elezbyl/usb-hub/hw/mcu.kicad_sch

## KiCad design hw/mcu.kicad_sch (2024-12-16)

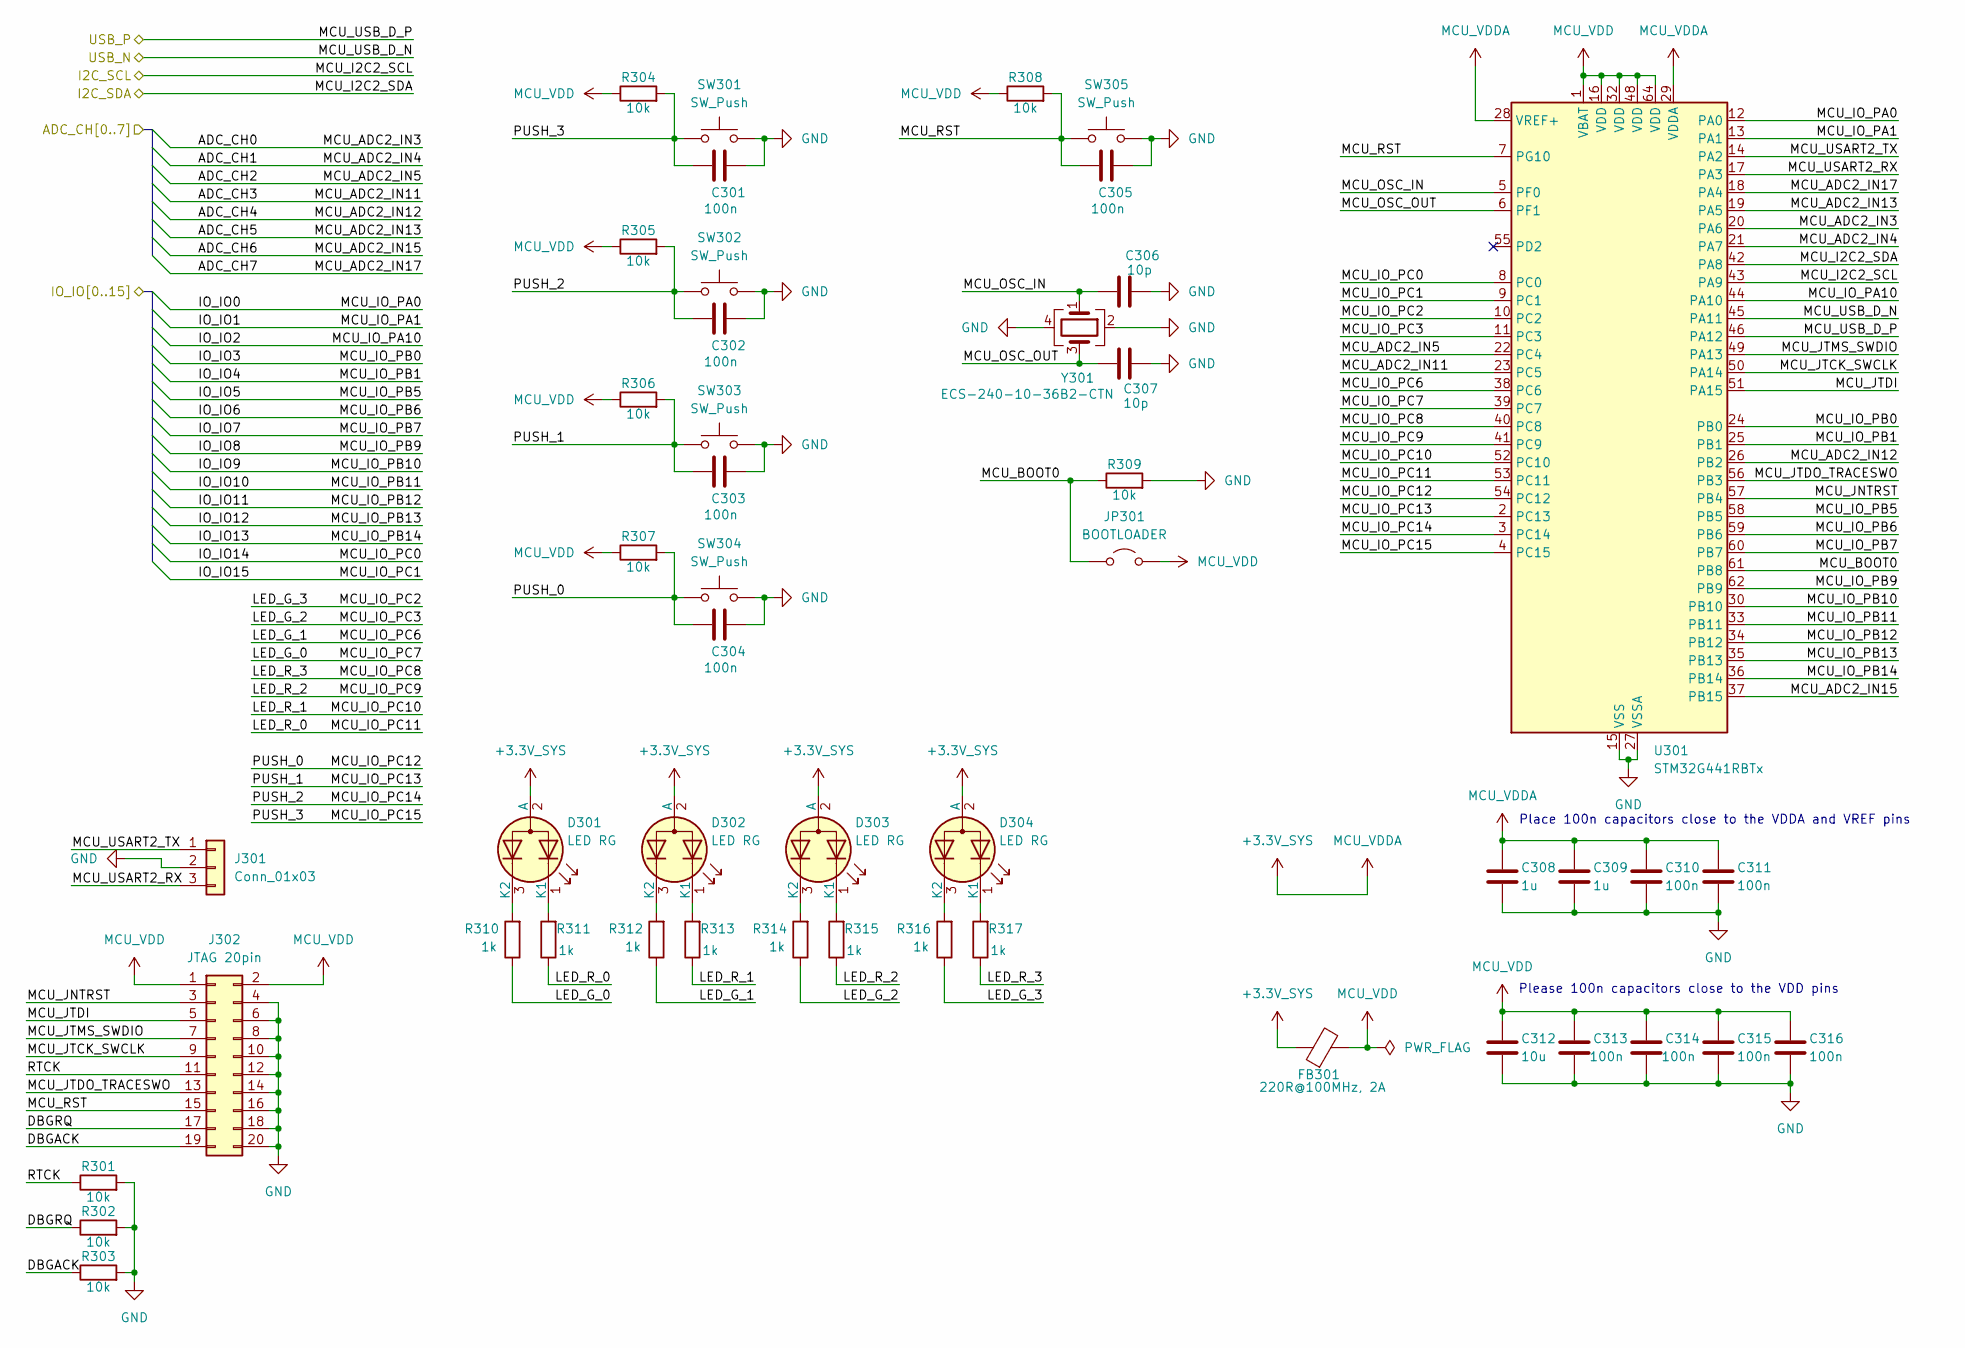
[picture p2: schematic mcu.kicad_sch]

Parts:
C301, C302, C303, C304, C305, C310, C311, C313, C314, C315, C316: 100n; C_0603_1608Metric_Pad1.08x0.95mm_HandSolder
C306, C307: 10p; C_0603_1608Metric_Pad1.08x0.95mm_HandSolder
C308, C309: 1u; C_0603_1608Metric_Pad1.08x0.95mm_HandSolder
C312: 10u; C_0805_2012Metric_Pad1.18x1.45mm_HandSolder
D301, D302, D303, D304: LED RG; LED_Wurth_155124RV73200; Farnell 2764997
FB301: 220R@100MHz, 2A; L_0805_2012Metric_Pad1.05x1.20mm_HandSolder; Farnell 1515661
J301: Conn_01x03; PinHeader_1x03_P2.54mm_Vertical
J302: JTAG 20pin; PinHeader_2x10_P2.54mm_Vertical
JP301: BOOTLOADER; PinHeader_1x02_P2.54mm_Vertical
R301, R302, R303, R304, R305, R306, R307, R308, R309: 10k; R_0603_1608Metric_Pad0.98x0.95mm_HandSolder
R310, R311, R312, R313, R314, R315, R316, R317: 1k; R_0603_1608Metric_Pad0.98x0.95mm_HandSolder
SW301, SW302, SW303, SW304, SW305: SW_Push; SW_Tactile_SPST_NO_Straight_CK_PTS636Sx25SMTRLFS; Farnell 3780601
U301: STM32G441RBTx; LQFP-64_10x10mm_P0.5mm; Farnell 3132415
Y301: ECS-240-10-36B2-CTN; Oscillator_SMD_ECS-xxx-x-36B2-xxx-4Pin_2.5x2.0mm; Farnell 4059099

Connections:
+3.3V_SYS: C308.1, C309.1, C310.1, C311.1, D301.2 (A), D302.2 (A), D303.2 (A), D304.2 (A), FB301.1, U301.28 (VREF+), U301.29 (VDDA)
ADC_CH0: U301.20 (PA6)
ADC_CH1: U301.21 (PA7)
ADC_CH2: U301.22 (PC4)
ADC_CH3: U301.23 (PC5)
ADC_CH4: U301.26 (PB2)
ADC_CH5: U301.19 (PA5)
ADC_CH6: U301.37 (PB15)
ADC_CH7: U301.18 (PA4)
DBGACK: J302.19, R303.1
DBGRQ: J302.17, R302.1
GND: C301.1, C302.1, C303.1, C304.1, C305.1, C306.1, C307.1, C308.2, C309.2, C310.2, C311.2, C312.2, C313.2, C314.2, C315.2, C316.2, J301.2, J302.4, J302.6, J302.8, J302.10, J302.12, J302.14, J302.16, J302.18, J302.20, R301.2, R302.2, R303.2, R309.2, SW301.2, SW302.2, SW303.2, SW304.2, SW305.2, U301.15 (VSS), U301.27 (VSSA), U301.31 (VSS), U301.47 (VSS), U301.63 (VSS), Y301.2, Y301.4
I2C_SCL: U301.43 (PA9)
I2C_SDA: U301.42 (PA8)
IO_IO0: U301.12 (PA0)
IO_IO1: U301.13 (PA1)
IO_IO2: U301.44 (PA10)
IO_IO3: U301.24 (PB0)
IO_IO4: U301.25 (PB1)
IO_IO5: U301.58 (PB5)
IO_IO6: U301.59 (PB6)
IO_IO7: U301.60 (PB7)
IO_IO8: U301.62 (PB9)
IO_IO9: U301.30 (PB10)
IO_IO10: U301.33 (PB11)
IO_IO11: U301.34 (PB12)
IO_IO12: U301.35 (PB13)
IO_IO13: U301.36 (PB14)
IO_IO14: U301.8 (PC0)
IO_IO15: U301.9 (PC1)
LED_G_0: R310.1, U301.39 (PC7)
LED_G_1: R312.1, U301.38 (PC6)
LED_G_2: R314.1, U301.11 (PC3)
LED_G_3: R316.1, U301.10 (PC2)
LED_R_0: R311.1, U301.53 (PC11)
LED_R_1: R313.1, U301.52 (PC10)
LED_R_2: R315.1, U301.41 (PC9)
LED_R_3: R317.1, U301.40 (PC8)
MCU_BOOT0: JP301.1 (A), R309.1, U301.61 (PB8)
MCU_IO_PC12: C304.2, R307.2, SW304.1, U301.54 (PC12)
MCU_IO_PC13: C303.2, R306.2, SW303.1, U301.2 (PC13)
MCU_IO_PC14: C302.2, R305.2, SW302.1, U301.3 (PC14)
MCU_IO_PC15: C301.2, R304.2, SW301.1, U301.4 (PC15)
MCU_JNTRST: J302.3, U301.57 (PB4)
MCU_JTCK_SWCLK: J302.9, U301.50 (PA14)
MCU_JTDI: J302.5, U301.51 (PA15)
MCU_JTDO_TRACESWO: J302.13, U301.56 (PB3)
MCU_JTMS_SWDIO: J302.7, U301.49 (PA13)
MCU_OSC_IN: C306.2, U301.5 (PF0), Y301.1
MCU_OSC_OUT: C307.2, U301.6 (PF1), Y301.3
MCU_RST: C305.2, J302.15, R308.2, SW305.1, U301.7 (PG10)
MCU_USART2_RX: J301.3, U301.17 (PA3)
MCU_USART2_TX: J301.1, U301.14 (PA2)
MCU_USB_D_N: U301.45 (PA11)
MCU_USB_D_P: U301.46 (PA12)
MCU_VDD: C312.1, C313.1, C314.1, C315.1, C316.1, FB301.2, J302.1, J302.2, JP301.2 (B), R304.1, R305.1, R306.1, R307.1, R308.1, U301.1 (VBAT), U301.16 (VDD), U301.32 (VDD), U301.48 (VDD), U301.64 (VDD)
unnamed: D301.1 (K1), R311.2
unnamed: D301.3 (K2), R310.2
unnamed: D302.1 (K1), R313.2
unnamed: D302.3 (K2), R312.2
unnamed: D303.1 (K1), R315.2
unnamed: D303.3 (K2), R314.2
unnamed: D304.1 (K1), R317.2
unnamed: D304.3 (K2), R316.2
RTCK: J302.11, R301.1

Notes on the sheet:
Please 100n capacitors close to the VDD pins
Place 100n capacitors close to the VDDA and VREF pins
