elezbyl/usb-hub/hw/power.kicad_sch

## KiCad design hw/power.kicad_sch (2024-12-16)

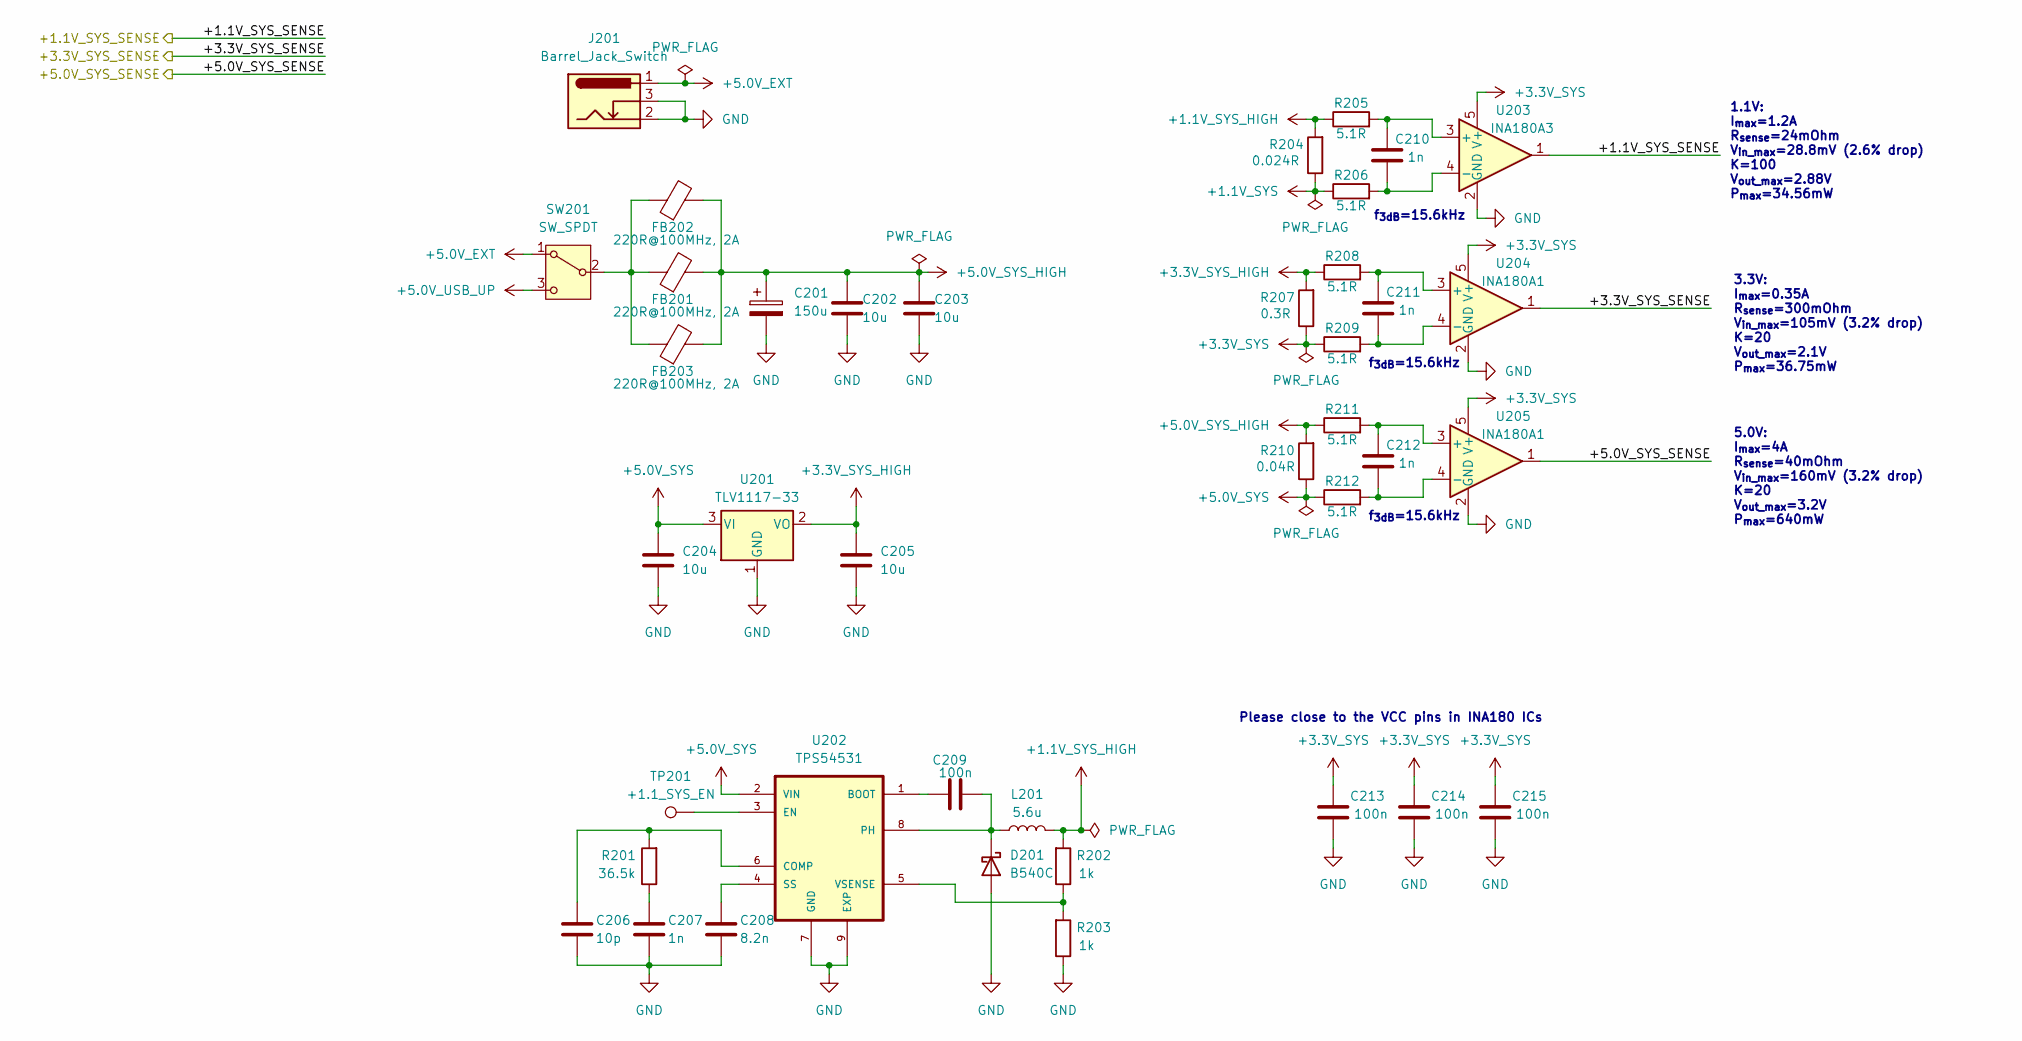
[picture p3: schematic power.kicad_sch]

Parts:
C201: 150u; CP_Elec_6.3x7.7; Farnell 2466196
C202, C203, C204, C205: 10u; C_0805_2012Metric_Pad1.18x1.45mm_HandSolder
C206: 10p; C_0603_1608Metric_Pad1.08x0.95mm_HandSolder
C207, C210, C211, C212: 1n; C_0603_1608Metric_Pad1.08x0.95mm_HandSolder
C208: 8.2n; C_0603_1608Metric_Pad1.08x0.95mm_HandSolder
C209, C213, C214, C215: 100n; C_0603_1608Metric_Pad1.08x0.95mm_HandSolder
D201: B540C; D_SMC_Handsoldering; Farnell 2306123
FB201, FB202, FB203: 220R@100MHz, 2A; L_0805_2012Metric_Pad1.05x1.20mm_HandSolder; Farnell 1515661
J201: Barrel_Jack_Switch; BarrelJack_Wuerth_6941xx301002; Farnell 2472149
L201: 5.6u; L_Bourns_SRP6540_7.2x6.5mm_HandSolder; Farnell 2309901
R201: 36.5k; R_0603_1608Metric_Pad0.98x0.95mm_HandSolder
R202, R203: 1k; R_0603_1608Metric_Pad0.98x0.95mm_HandSolder
R204: 0.024R; R_1206_3216Metric_Pad1.30x1.75mm_HandSolder; Mouser L4CL1206LR024DNR
R205, R206, R208, R209, R211, R212: 5.1R; R_0603_1608Metric_Pad0.98x0.95mm_HandSolder
R207: 0.3R; R_1206_3216Metric_Pad1.30x1.75mm_HandSolder; Farnell 4015842
R210: 0.04R; R_1206_3216Metric_Pad1.30x1.75mm_HandSolder; Mouser 71-WSLP1206R0400DEA
SW201: SW_SPDT; PinHeader_1x03_P2.54mm_Vertical
TP201: +1.1_SYS_EN; TestPoint_Pad_D2.5mm
U201: TLV1117-33; SOT-223-3_TabPin2; Farnell 3122356
U202: TPS54531; Texas_R-PDSO-G8_EP2.95x4.9mm_Mask2.4x3.1mm_ThermalVias; Farnell 3007357
U203: INA180A3; SOT-23-5; Farnell 3005321
U204, U205: INA180A1; SOT-23-5; Farnell 3118130

Connections:
+1.1V_SYS: R204.1, R206.1
+1.1V_SYS_HIGH: L201.2, R202.2, R204.2, R205.1
+1.1V_SYS_SENSE: U203.1
+3.3V_SYS: C213.2, C214.2, C215.2, R207.1, R209.1, U203.5 (V+), U204.5 (V+), U205.5 (V+)
+3.3V_SYS_HIGH: C205.1, R207.2, R208.1, U201.2 (VO)
+3.3V_SYS_SENSE: U204.1
+5.0V_EXT: J201.1, SW201.1 (A)
+5.0V_SYS: C204.1, R210.1, R212.1, U201.3 (VI), U202.2 (VIN)
+5.0V_SYS_HIGH: C201.1, C202.1, C203.1, FB201.2, FB202.2, FB203.2, R210.2, R211.1
+5.0V_SYS_SENSE: U205.1
+5.0V_USB_UP: SW201.3 (C)
GND: C201.2, C202.2, C203.2, C204.2, C205.2, C206.2, C207.2, C208.2, C213.1, C214.1, C215.1, D201.2 (A), J201.2, J201.3, R203.1, U201.1 (GND), U202.7 (GND), U202.9 (EXP), U203.2 (GND), U204.2 (GND), U205.2 (GND)
unnamed: C206.1, R201.2, U202.6 (COMP)
unnamed: C207.1, R201.1
unnamed: C208.1, U202.4 (SS)
unnamed: C209.1, U202.1 (BOOT)
unnamed: C209.2, D201.1 (K), L201.1, U202.8 (PH)
unnamed: C210.1, R206.2, U203.4 (-)
unnamed: C210.2, R205.2, U203.3 (+)
unnamed: C211.1, R209.2, U204.4 (-)
unnamed: C211.2, R208.2, U204.3 (+)
unnamed: C212.1, R212.2, U205.4 (-)
unnamed: C212.2, R211.2, U205.3 (+)
unnamed: FB201.1, FB202.1, FB203.1, SW201.2 (B)
unnamed: R202.1, R203.2, U202.5 (VSENSE)
unnamed: TP201.1, U202.3 (EN)

Notes on the sheet:
f_{3dB}=15.6kHz
5.0V: I_{max}=4A R_{sense}=40mOhm V_{in_max}=160mV (3.2% drop) K=20 V_{out_max}=3.2V P_{max}=640mW
3.3V: I_{max}=0.35A R_{sense}=300mOhm V_{in_max}=105mV (3.2% drop) K=20 V_{out_max}=2.1V P_{max}=36.75mW
Please close to the VCC pins in INA180 ICs
1.1V: I_{max}=1.2A R_{sense}=24mOhm V_{in_max}=28.8mV (2.6% drop) K=100 V_{out_max}=2.88V P_{max}=34.56mW
