elezbyl/usb-hub/hw/usb-downstream.kicad_sch

## KiCad design hw/usb-downstream.kicad_sch (2024-12-16)

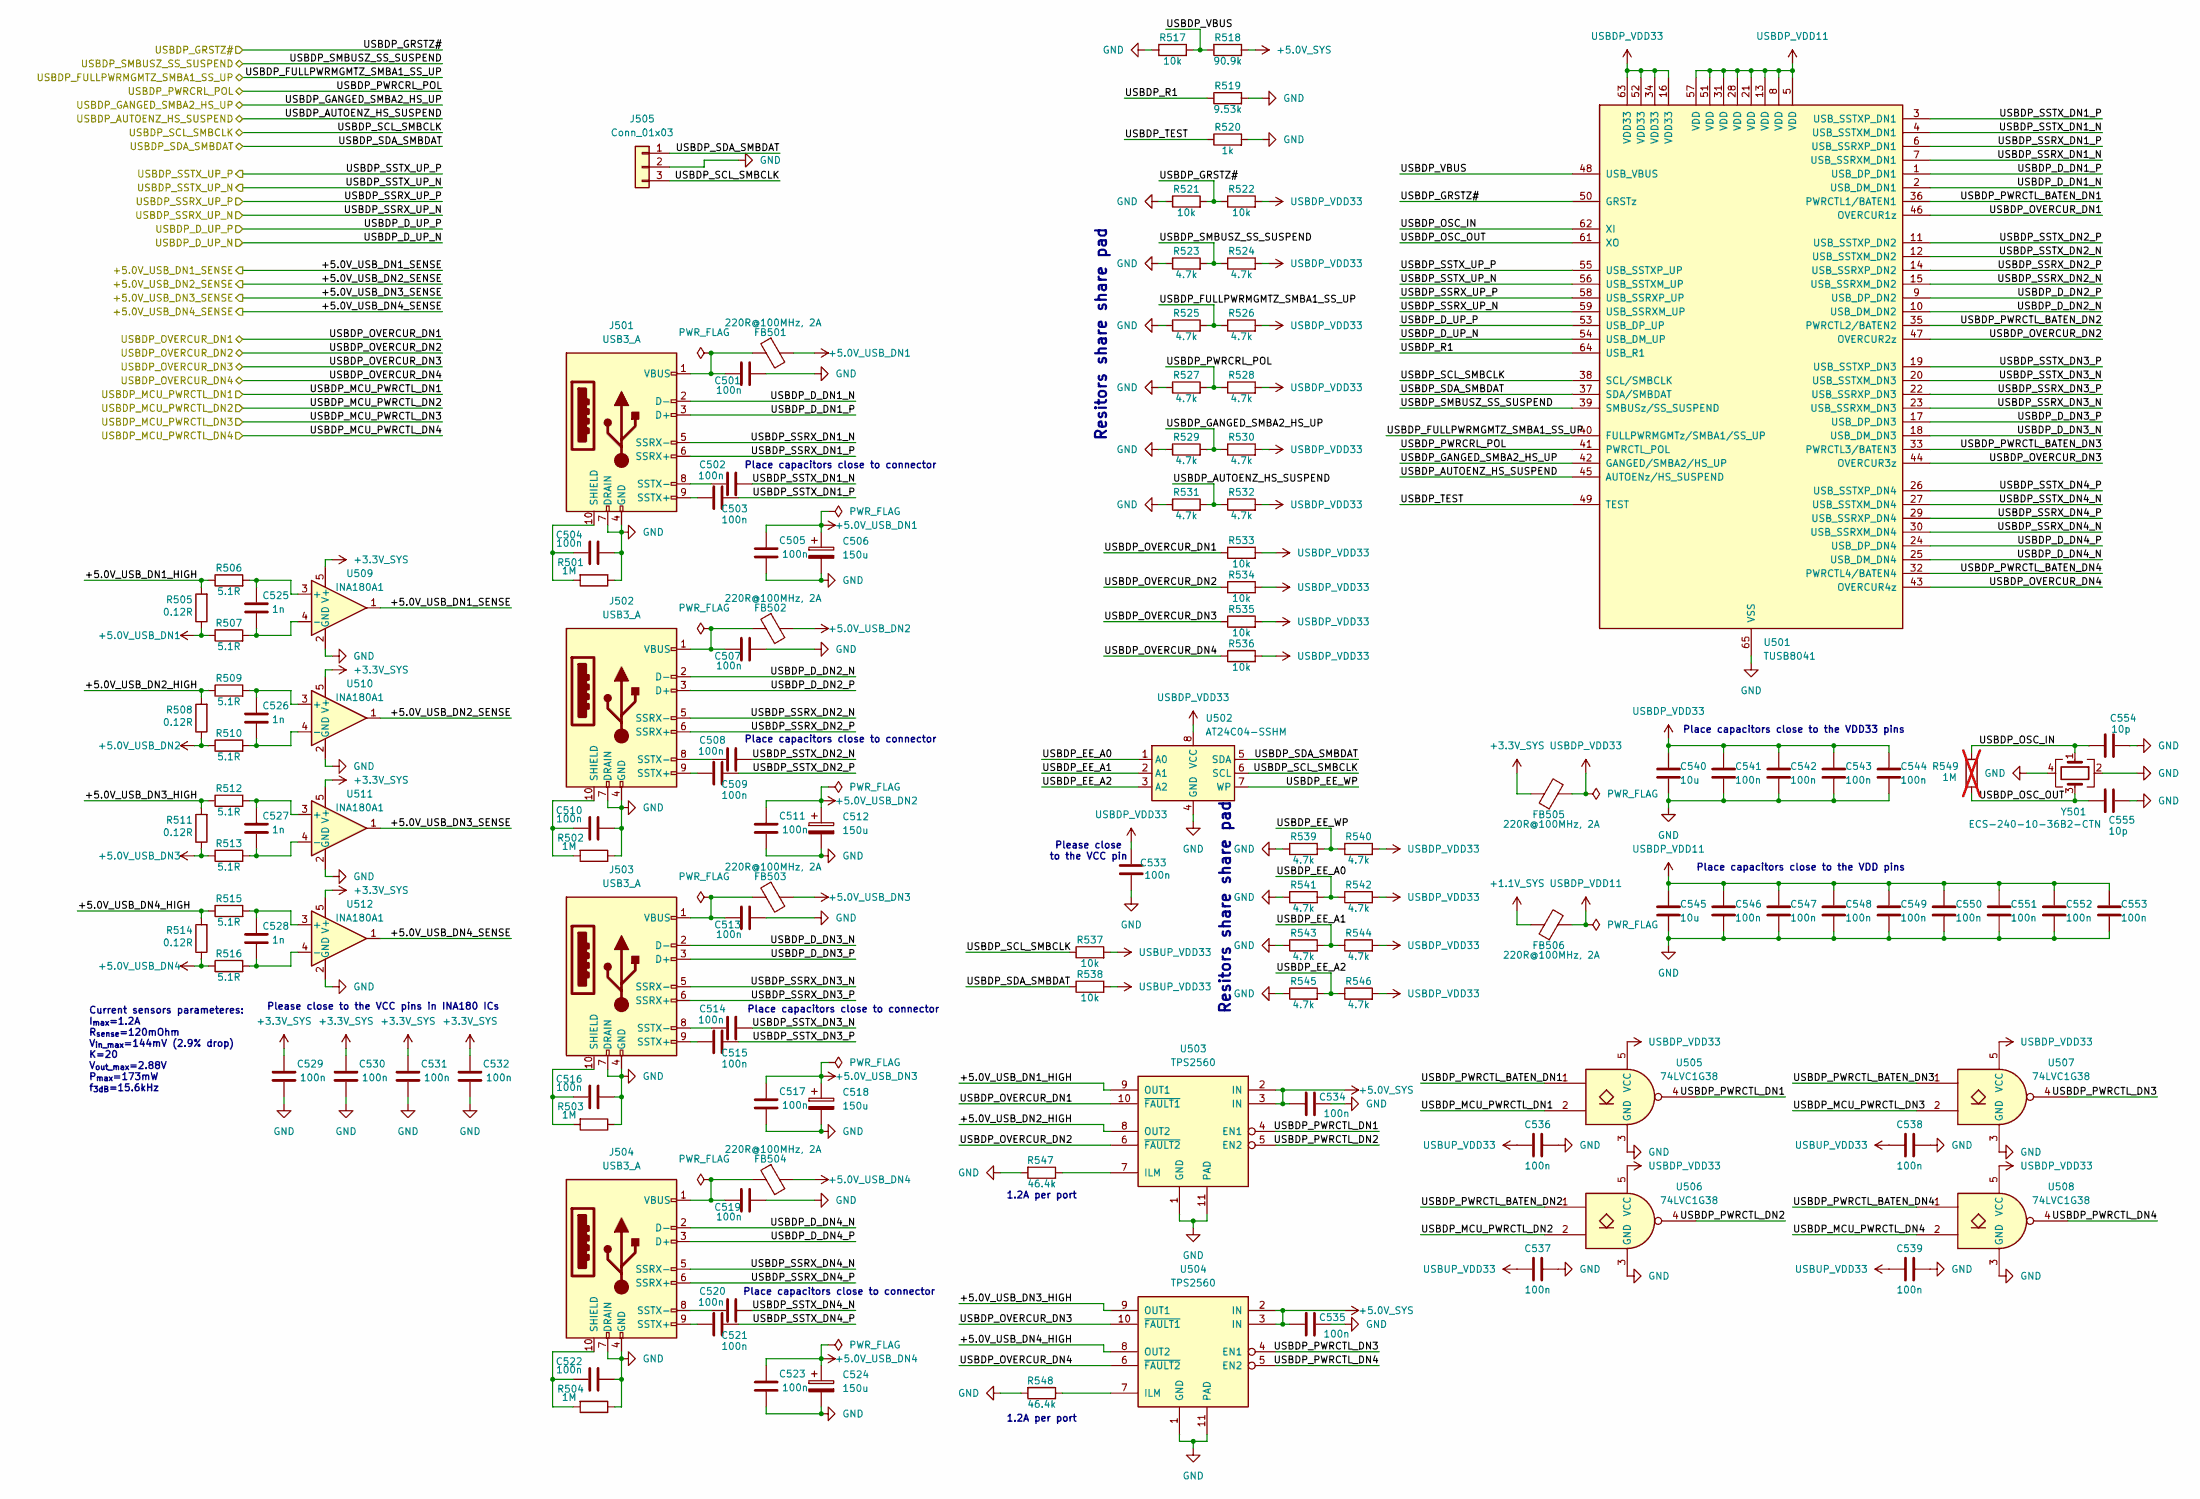
[picture p4: schematic usb-downstream.kicad_sch]

Parts:
C501, C504, C505, C507, C510, C511, C513, C516, C517, C519, C522, C523, C529, C530, C531, C532, C533, C534, C535, C536, C537, C538, C539, C541, C542, C543, C544, C546, C547, C548, C549, C550, C551, C552, C553: 100n; C_0603_1608Metric_Pad1.08x0.95mm_HandSolder
C502, C503, C508, C509, C514, C515, C520, C521: 100n; C_0402_1005Metric_Pad0.74x0.62mm_HandSolder
C506, C512, C518, C524: 150u; CP_Elec_6.3x7.7; Farnell 2466196
C525, C526, C527, C528: 1n; C_0603_1608Metric_Pad1.08x0.95mm_HandSolder
C540, C545: 10u; C_0805_2012Metric_Pad1.18x1.45mm_HandSolder
C554, C555: 10p; C_0603_1608Metric_Pad1.08x0.95mm_HandSolder
FB501, FB502, FB503, FB504, FB505, FB506: 220R@100MHz, 2A; L_0805_2012Metric_Pad1.05x1.20mm_HandSolder; Farnell 1515661
J501, J502, J503, J504: USB3_A; USB_A_Amphenol_GSB3111xxxHR; Farnell 3882406
J505: Conn_01x03; PinHeader_1x03_P2.54mm_Vertical
R501, R502, R503, R504: 1M; R_0603_1608Metric_Pad0.98x0.95mm_HandSolder
R505, R508, R511, R514: 0.12R; R_1206_3216Metric_Pad1.30x1.75mm_HandSolder; Farnell 4045438
R506, R507, R509, R510, R512, R513, R515, R516: 5.1R; R_0603_1608Metric_Pad0.98x0.95mm_HandSolder
R517, R521, R522, R533, R534, R535, R536, R537, R538: 10k; R_0603_1608Metric_Pad0.98x0.95mm_HandSolder
R518: 90.9k; R_0603_1608Metric_Pad0.98x0.95mm_HandSolder
R519: 9.53k; R_0603_1608Metric_Pad0.98x0.95mm_HandSolder
R520: 1k; R_0603_1608Metric_Pad0.98x0.95mm_HandSolder
R523, R524, R525, R526, R527, R528, R529, R530, R531, R532, R539, R540, R541, R542, R543, R544, R545, R546: 4.7k; R_0603_1608Metric_Pad0.98x0.95mm_HandSolder
R547, R548: 46.4k; R_0603_1608Metric_Pad0.98x0.95mm_HandSolder
R549: 1M; R_0603_1608Metric_Pad0.98x0.95mm_HandSolder; not fitted
U501: TUSB8041; QFN-64-1EP_9x9mm_P0.5mm_EP6x6mm_ThermalVias; Mouser 595-TUSB8041RGCR
U502: AT24C04-SSHM; SOIC-8_3.9x4.9mm_P1.27mm; Farnell 2345581
U503, U504: TPS2560; VSON-10-1EP_3x3mm_P0.5mm_EP1.65x2.4mm_ThermalVias; Mouser 595-TPS2560DRCR
U505, U506, U507, U508: 74LVC1G38; SOT-353_SC-70-5_Handsoldering; Farnell 3442031
U509, U510, U511, U512: INA180A1; SOT-23-5; Farnell 3118130
Y501: ECS-240-10-36B2-CTN; Oscillator_SMD_ECS-xxx-x-36B2-xxx-4Pin_2.5x2.0mm; Farnell 4059099

Connections:
+1.1V_SYS: FB506.1
+3.3V_SYS: C529.2, C530.2, C531.2, C532.2, FB505.1, U509.5 (V+), U510.5 (V+), U511.5 (V+), U512.5 (V+)
+5.0V_SYS: C534.2, C535.2, R518.2, U503.2 (IN), U503.3 (IN), U504.2 (IN), U504.3 (IN)
+5.0V_USB_DN1: C505.2, C506.1, FB501.2, R505.1, R507.1
+5.0V_USB_DN1_HIGH: R505.2, R506.1, U503.9 (OUT1)
+5.0V_USB_DN1_SENSE: U509.1
+5.0V_USB_DN2: C511.2, C512.1, FB502.2, R508.1, R510.1
+5.0V_USB_DN2_HIGH: R508.2, R509.1, U503.8 (OUT2)
+5.0V_USB_DN2_SENSE: U510.1
+5.0V_USB_DN3: C517.2, C518.1, FB503.2, R511.1, R513.1
+5.0V_USB_DN3_HIGH: R511.2, R512.1, U504.9 (OUT1)
+5.0V_USB_DN3_SENSE: U511.1
+5.0V_USB_DN4: C523.2, C524.1, FB504.2, R514.1, R516.1
+5.0V_USB_DN4_HIGH: R514.2, R515.1, U504.8 (OUT2)
+5.0V_USB_DN4_SENSE: U512.1
GND: C501.1, C504.1, C505.1, C506.2, C507.1, C510.1, C511.1, C512.2, C513.1, C516.1, C517.1, C518.2, C519.1, C522.1, C523.1, C524.2, C529.1, C530.1, C531.1, C532.1, C533.2, C534.1, C535.1, C536.2, C537.2, C538.2, C539.2, C540.2, C541.2, C542.2, C543.2, C544.2, C545.2, C546.2, C547.2, C548.2, C549.2, C550.2, C551.2, C552.2, C553.2, C554.1, C555.1, J501.4 (GND), J501.7 (DRAIN), J502.4 (GND), J502.7 (DRAIN), J503.4 (GND), J503.7 (DRAIN), J504.4 (GND), J504.7 (DRAIN), J505.2, R501.1, R502.1, R503.1, R504.1, R517.1, R519.2, R520.2, R521.1, R523.1, R525.1, R527.1, R529.1, R531.1, R539.1, R541.1, R543.1, R545.1, R547.2, R548.2, U501.65 (VSS), U502.4 (GND), U503.1 (GND), U503.11 (PAD), U504.1 (GND), U504.11 (PAD), U505.3 (GND), U506.3 (GND), U507.3 (GND), U508.3 (GND), U509.2 (GND), U510.2 (GND), U511.2 (GND), U512.2 (GND), Y501.2, Y501.4
unnamed: C501.2, FB501.1, J501.1 (VBUS)
unnamed: C502.2, J501.8 (SSTX-)
unnamed: C503.2, J501.9 (SSTX+)
unnamed: C504.2, J501.10 (SHIELD), R501.2
unnamed: C507.2, FB502.1, J502.1 (VBUS)
unnamed: C508.2, J502.8 (SSTX-)
unnamed: C509.2, J502.9 (SSTX+)
unnamed: C510.2, J502.10 (SHIELD), R502.2
unnamed: C513.2, FB503.1, J503.1 (VBUS)
unnamed: C514.2, J503.8 (SSTX-)
unnamed: C515.2, J503.9 (SSTX+)
unnamed: C516.2, J503.10 (SHIELD), R503.2
unnamed: C519.2, FB504.1, J504.1 (VBUS)
unnamed: C520.2, J504.8 (SSTX-)
unnamed: C521.2, J504.9 (SSTX+)
unnamed: C522.2, J504.10 (SHIELD), R504.2
unnamed: C525.1, R507.2, U509.4 (-)
unnamed: C525.2, R506.2, U509.3 (+)
unnamed: C526.1, R510.2, U510.4 (-)
unnamed: C526.2, R509.2, U510.3 (+)
unnamed: C527.1, R513.2, U511.4 (-)
unnamed: C527.2, R512.2, U511.3 (+)
unnamed: C528.1, R516.2, U512.4 (-)
unnamed: C528.2, R515.2, U512.3 (+)
unnamed: R547.1, U503.7 (ILM)
unnamed: R548.1, U504.7 (ILM)
USBDP_AUTOENZ_HS_SUSPEND: R531.2, R532.1, U501.45 (AUTOENz/HS_SUSPEND)
USBDP_D_DN1_N: J501.2 (D-), U501.2 (USB_DM_DN1)
USBDP_D_DN1_P: J501.3 (D+), U501.1 (USB_DP_DN1)
USBDP_D_DN2_N: J502.2 (D-), U501.10 (USB_DM_DN2)
USBDP_D_DN2_P: J502.3 (D+), U501.9 (USB_DP_DN2)
USBDP_D_DN3_N: J503.2 (D-), U501.18 (USB_DM_DN3)
USBDP_D_DN3_P: J503.3 (D+), U501.17 (USB_DP_DN3)
USBDP_D_DN4_N: J504.2 (D-), U501.25 (USB_DM_DN4)
USBDP_D_DN4_P: J504.3 (D+), U501.24 (USB_DP_DN4)
USBDP_D_UP_N: U501.54 (USB_DM_UP)
USBDP_D_UP_P: U501.53 (USB_DP_UP)
USBDP_EE_A0: R541.2, R542.1, U502.1 (A0)
USBDP_EE_A1: R543.2, R544.1, U502.2 (A1)
USBDP_EE_A2: R545.2, R546.1, U502.3 (A2)
USBDP_EE_WP: R539.2, R540.1, U502.7 (WP)
USBDP_FULLPWRMGMTZ_SMBA1_SS_UP: R525.2, R526.1, U501.40 (FULLPWRMGMTz/SMBA1/SS_UP)
USBDP_GANGED_SMBA2_HS_UP: R529.2, R530.1, U501.42 (GANGED/SMBA2/HS_UP)
USBDP_GRSTZ#: R521.2, R522.1, U501.50 (GRSTz)
USBDP_MCU_PWRCTL_DN1: U505.2
USBDP_MCU_PWRCTL_DN2: U506.2
USBDP_MCU_PWRCTL_DN3: U507.2
USBDP_MCU_PWRCTL_DN4: U508.2
USBDP_OSC_IN: C554.2, R549.2, U501.62 (XI), Y501.1
USBDP_OSC_OUT: C555.2, R549.1, U501.61 (XO), Y501.3
USBDP_OVERCUR_DN1: R533.1, U501.46 (OVERCUR1z), U503.10 (~FAULT1)
USBDP_OVERCUR_DN2: R534.1, U501.47 (OVERCUR2z), U503.6 (~FAULT2)
USBDP_OVERCUR_DN3: R535.1, U501.44 (OVERCUR3z), U504.10 (~FAULT1)
USBDP_OVERCUR_DN4: R536.1, U501.43 (OVERCUR4z), U504.6 (~FAULT2)
USBDP_PWRCRL_POL: R527.2, R528.1, U501.41 (PWRCTL_POL)
USBDP_PWRCTL_BATEN_DN1: U501.36 (PWRCTL1/BATEN1), U505.1
USBDP_PWRCTL_BATEN_DN2: U501.35 (PWRCTL2/BATEN2), U506.1
USBDP_PWRCTL_BATEN_DN3: U501.33 (PWRCTL3/BATEN3), U507.1
USBDP_PWRCTL_BATEN_DN4: U501.32 (PWRCTL4/BATEN4), U508.1
USBDP_PWRCTL_DN1: U503.4 (EN1), U505.4
USBDP_PWRCTL_DN2: U503.5 (EN2), U506.4
USBDP_PWRCTL_DN3: U504.4 (EN1), U507.4
USBDP_PWRCTL_DN4: U504.5 (EN2), U508.4
USBDP_R1: R519.1, U501.64 (USB_R1)
USBDP_SCL_SMBCLK: J505.3, R537.1, U501.38 (SCL/SMBCLK), U502.6 (SCL)
USBDP_SDA_SMBDAT: J505.1, R538.1, U501.37 (SDA/SMBDAT), U502.5 (SDA)
USBDP_SMBUSZ_SS_SUSPEND: R523.2, R524.1, U501.39 (SMBUSz/SS_SUSPEND)
USBDP_SSRX_DN1_N: J501.5 (SSRX-), U501.7 (USB_SSRXM_DN1)
USBDP_SSRX_DN1_P: J501.6 (SSRX+), U501.6 (USB_SSRXP_DN1)
USBDP_SSRX_DN2_N: J502.5 (SSRX-), U501.15 (USB_SSRXM_DN2)
USBDP_SSRX_DN2_P: J502.6 (SSRX+), U501.14 (USB_SSRXP_DN2)
USBDP_SSRX_DN3_N: J503.5 (SSRX-), U501.23 (USB_SSRXM_DN3)
USBDP_SSRX_DN3_P: J503.6 (SSRX+), U501.22 (USB_SSRXP_DN3)
USBDP_SSRX_DN4_N: J504.5 (SSRX-), U501.30 (USB_SSRXM_DN4)
USBDP_SSRX_DN4_P: J504.6 (SSRX+), U501.29 (USB_SSRXP_DN4)
USBDP_SSRX_UP_N: U501.59 (USB_SSRXM_UP)
USBDP_SSRX_UP_P: U501.58 (USB_SSRXP_UP)
USBDP_SSTX_DN1_N: C502.1, U501.4 (USB_SSTXM_DN1)
USBDP_SSTX_DN1_P: C503.1, U501.3 (USB_SSTXP_DN1)
USBDP_SSTX_DN2_N: C508.1, U501.12 (USB_SSTXM_DN2)
USBDP_SSTX_DN2_P: C509.1, U501.11 (USB_SSTXP_DN2)
USBDP_SSTX_DN3_N: C514.1, U501.20 (USB_SSTXM_DN3)
USBDP_SSTX_DN3_P: C515.1, U501.19 (USB_SSTXP_DN3)
USBDP_SSTX_DN4_N: C520.1, U501.27 (USB_SSTXM_DN4)
USBDP_SSTX_DN4_P: C521.1, U501.26 (USB_SSTXP_DN4)
USBDP_SSTX_UP_N: U501.56 (USB_SSTXM_UP)
USBDP_SSTX_UP_P: U501.55 (USB_SSTXP_UP)
USBDP_TEST: R520.1, U501.49 (TEST)
USBDP_VBUS: R517.2, R518.1, U501.48 (USB_VBUS)
USBDP_VDD11: C545.1, C546.1, C547.1, C548.1, C549.1, C550.1, C551.1, C552.1, C553.1, FB506.2, U501.5 (VDD), U501.8 (VDD), U501.13 (VDD), U501.21 (VDD), U501.28 (VDD), U501.31 (VDD), U501.51 (VDD), U501.57 (VDD)
USBDP_VDD33: C533.1, C540.1, C541.1, C542.1, C543.1, C544.1, FB505.2, R522.2, R524.2, R526.2, R528.2, R530.2, R532.2, R533.2, R534.2, R535.2, R536.2, R540.2, R542.2, R544.2, R546.2, U501.16 (VDD33), U501.34 (VDD33), U501.52 (VDD33), U501.63 (VDD33), U502.8 (VCC), U505.5 (VCC), U506.5 (VCC), U507.5 (VCC), U508.5 (VCC)
USBUP_VDD33: C536.1, C537.1, C538.1, C539.1, R537.2, R538.2

Notes on the sheet:
Resitors share share pad
Place capacitors close to connector
Place capacitors close to the VDD pins
1.2A per port
Please close to the VCC pin
Place capacitors close to the VDD33 pins
Current sensors parameteres: I_{max}=1.2A R_{sense}=120mOhm V_{in_max}=144mV (2.9% drop) K=20 V_{out_max}=2.88V P_{max}=173mW f_{3dB}=15.6kHz
Please close to the VCC pins in INA180 ICs
