elezbyl/usb-hub/hw/usb-upstream.kicad_sch

## KiCad design hw/usb-upstream.kicad_sch (2024-12-16)

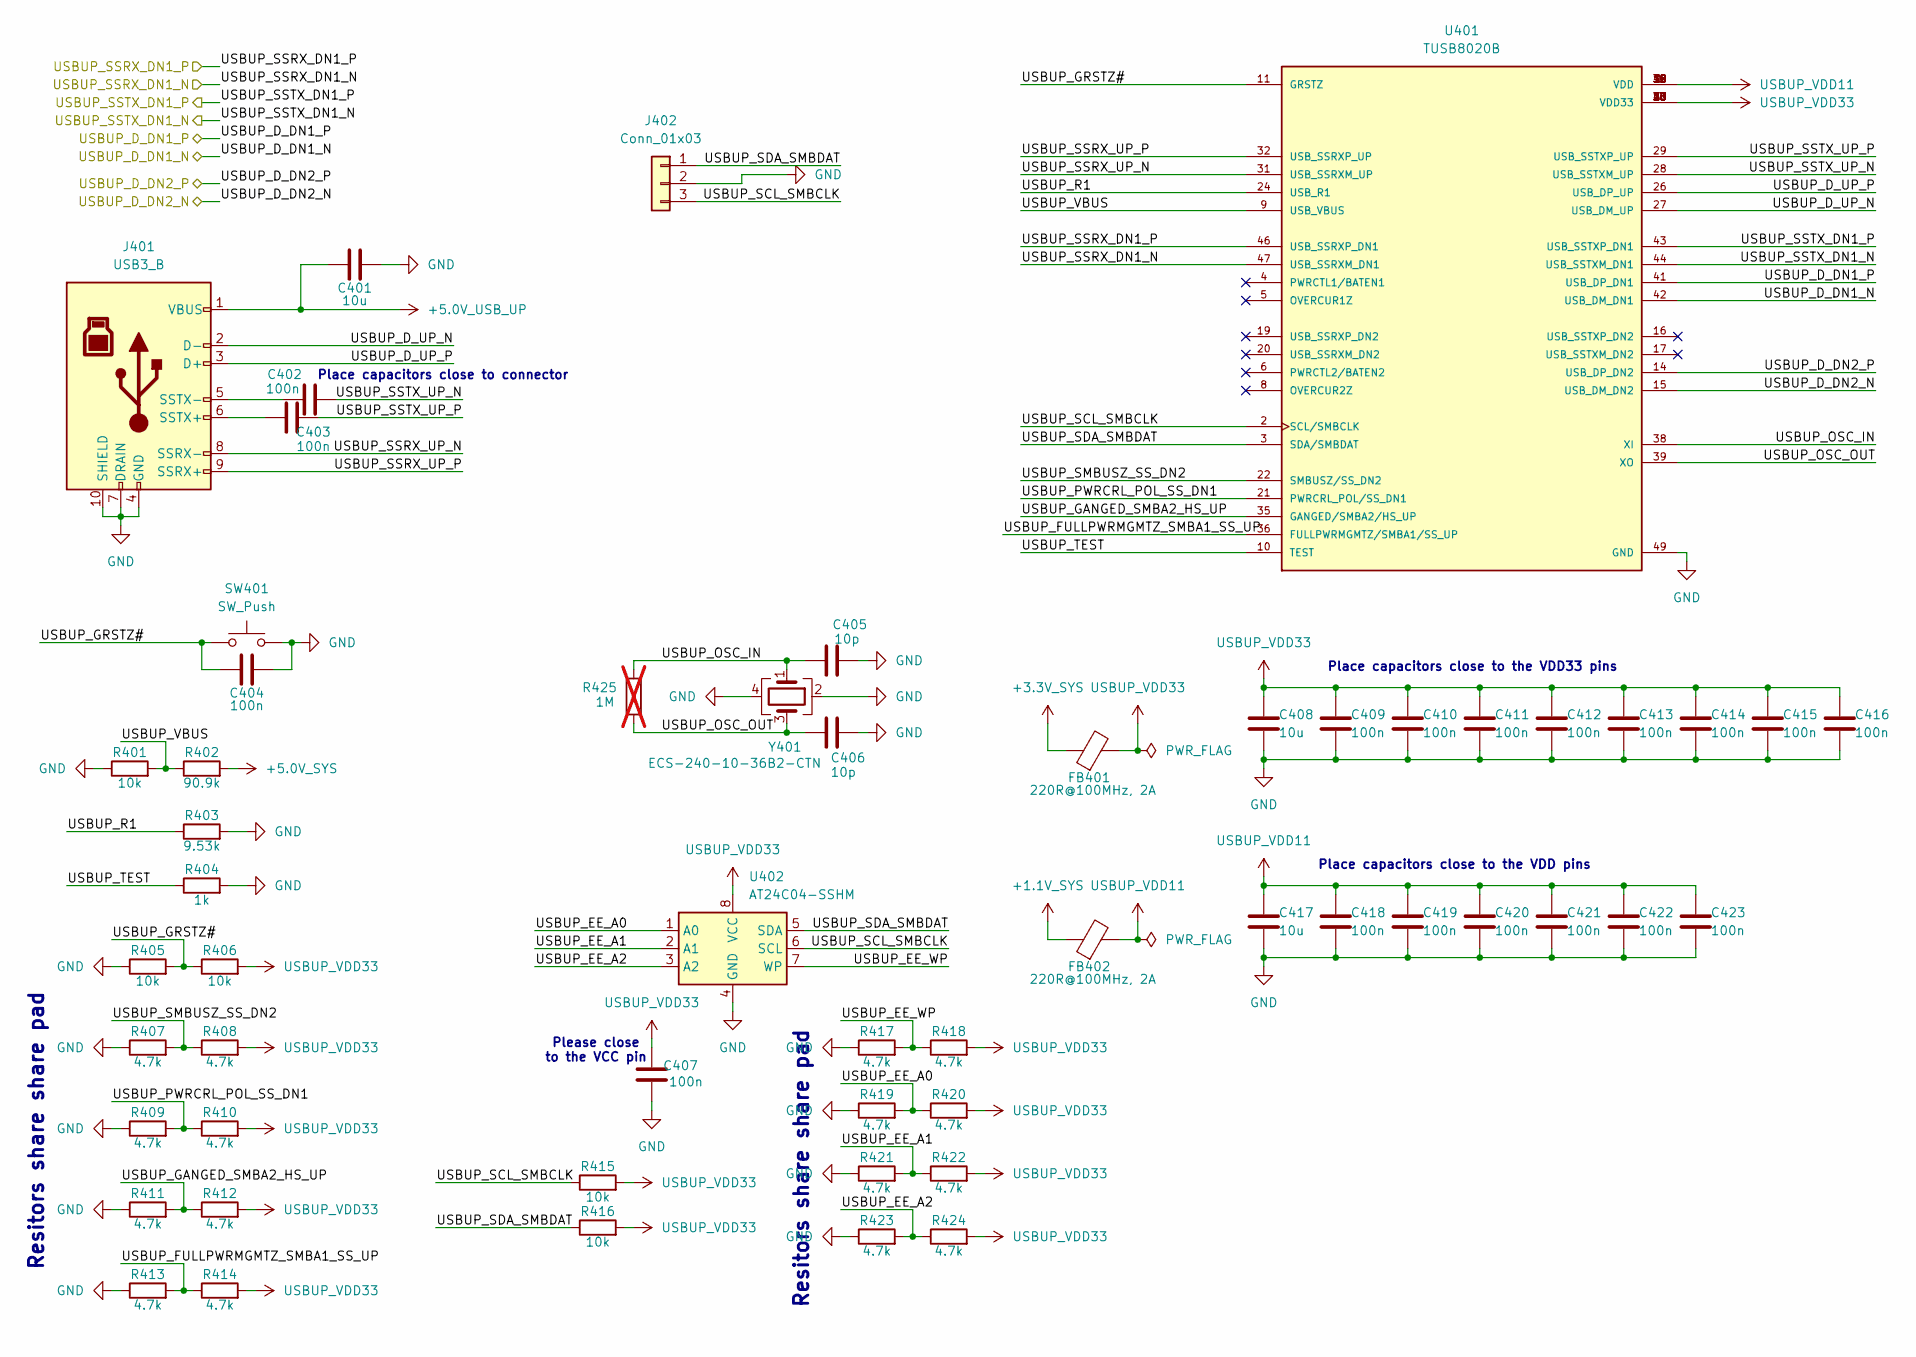
[picture p5: schematic usb-upstream.kicad_sch]

Parts:
C401: 10u; C_0603_1608Metric_Pad1.08x0.95mm_HandSolder
C402, C403: 100n; C_0402_1005Metric_Pad0.74x0.62mm_HandSolder
C404, C407, C409, C410, C411, C412, C413, C414, C415, C416, C418, C419, C420, C421, C422, C423: 100n; C_0603_1608Metric_Pad1.08x0.95mm_HandSolder
C405, C406: 10p; C_0603_1608Metric_Pad1.08x0.95mm_HandSolder
C408, C417: 10u; C_0805_2012Metric_Pad1.18x1.45mm_HandSolder
FB401, FB402: 220R@100MHz, 2A; L_0805_2012Metric_Pad1.05x1.20mm_HandSolder; Farnell 1515661
J401: USB3_B; USB_B_Amphenol_GSB3211xxxWEU; Farnell 3367999
J402: Conn_01x03; PinHeader_1x03_P2.54mm_Vertical
R401, R405, R406, R415, R416: 10k; R_0603_1608Metric_Pad0.98x0.95mm_HandSolder
R402: 90.9k; R_0603_1608Metric_Pad0.98x0.95mm_HandSolder
R403: 9.53k; R_0603_1608Metric_Pad0.98x0.95mm_HandSolder
R404: 1k; R_0603_1608Metric_Pad0.98x0.95mm_HandSolder
R407, R408, R409, R410, R411, R412, R413, R414, R417, R418, R419, R420, R421, R422, R423, R424: 4.7k; R_0603_1608Metric_Pad0.98x0.95mm_HandSolder
R425: 1M; R_0603_1608Metric_Pad0.98x0.95mm_HandSolder; not fitted
SW401: SW_Push; SW_Tactile_SPST_NO_Straight_CK_PTS636Sx25SMTRLFS; Farnell 3780601
U401: TUSB8020B; HTQFP-48-7x7mm-P0.5mm-EP7x7mm; Mouser 595-TUSB8020BPHPR
U402: AT24C04-SSHM; SOIC-8_3.9x4.9mm_P1.27mm; Farnell 2345581
Y401: ECS-240-10-36B2-CTN; Oscillator_SMD_ECS-xxx-x-36B2-xxx-4Pin_2.5x2.0mm; Farnell 4059099

Connections:
+1.1V_SYS: FB402.1
+3.3V_SYS: FB401.1
+5.0V_SYS: R402.2
+5.0V_USB_UP: C401.2, J401.1 (VBUS)
GND: C401.1, C404.1, C405.1, C406.1, C407.2, C408.2, C409.2, C410.2, C411.2, C412.2, C413.2, C414.2, C415.2, C416.2, C417.2, C418.2, C419.2, C420.2, C421.2, C422.2, C423.2, J401.4 (GND), J401.7 (DRAIN), J401.10 (SHIELD), J402.2, R401.1, R403.2, R404.2, R405.1, R407.1, R409.1, R411.1, R413.1, R417.1, R419.1, R421.1, R423.1, SW401.2, U401.49 (GND), U402.4 (GND), Y401.2, Y401.4
unnamed: C402.2, J401.5 (SSTX-)
unnamed: C403.2, J401.6 (SSTX+)
USBUP_D_DN1_N: U401.42 (USB_DM_DN1)
USBUP_D_DN1_P: U401.41 (USB_DP_DN1)
USBUP_D_DN2_N: U401.15 (USB_DM_DN2)
USBUP_D_DN2_P: U401.14 (USB_DP_DN2)
USBUP_D_UP_N: J401.2 (D-), U401.27 (USB_DM_UP)
USBUP_D_UP_P: J401.3 (D+), U401.26 (USB_DP_UP)
USBUP_EE_A0: R419.2, R420.1, U402.1 (A0)
USBUP_EE_A1: R421.2, R422.1, U402.2 (A1)
USBUP_EE_A2: R423.2, R424.1, U402.3 (A2)
USBUP_EE_WP: R417.2, R418.1, U402.7 (WP)
USBUP_FULLPWRMGMTZ_SMBA1_SS_UP: R413.2, R414.1, U401.36 (FULLPWRMGMTZ/SMBA1/SS_UP)
USBUP_GANGED_SMBA2_HS_UP: R411.2, R412.1, U401.35 (GANGED/SMBA2/HS_UP)
USBUP_GRSTZ#: C404.2, R405.2, R406.1, SW401.1, U401.11 (GRSTZ)
USBUP_OSC_IN: C405.2, R425.2, U401.38 (XI), Y401.1
USBUP_OSC_OUT: C406.2, R425.1, U401.39 (XO), Y401.3
USBUP_PWRCRL_POL_SS_DN1: R409.2, R410.1, U401.21 (PWRCRL_POL/SS_DN1)
USBUP_R1: R403.1, U401.24 (USB_R1)
USBUP_SCL_SMBCLK: J402.3, R415.1, U401.2 (SCL/SMBCLK), U402.6 (SCL)
USBUP_SDA_SMBDAT: J402.1, R416.1, U401.3 (SDA/SMBDAT), U402.5 (SDA)
USBUP_SMBUSZ_SS_DN2: R407.2, R408.1, U401.22 (SMBUSZ/SS_DN2)
USBUP_SSRX_DN1_N: U401.47 (USB_SSRXM_DN1)
USBUP_SSRX_DN1_P: U401.46 (USB_SSRXP_DN1)
USBUP_SSRX_UP_N: J401.8 (SSRX-), U401.31 (USB_SSRXM_UP)
USBUP_SSRX_UP_P: J401.9 (SSRX+), U401.32 (USB_SSRXP_UP)
USBUP_SSTX_DN1_N: U401.44 (USB_SSTXM_DN1)
USBUP_SSTX_DN1_P: U401.43 (USB_SSTXP_DN1)
USBUP_SSTX_UP_N: C402.1, U401.28 (USB_SSTXM_UP)
USBUP_SSTX_UP_P: C403.1, U401.29 (USB_SSTXP_UP)
USBUP_TEST: R404.1, U401.10 (TEST)
USBUP_VBUS: R401.2, R402.1, U401.9 (USB_VBUS)
USBUP_VDD11: C417.1, C418.1, C419.1, C420.1, C421.1, C422.1, C423.1, FB402.2, U401.1 (VDD), U401.12 (VDD), U401.18 (VDD), U401.30 (VDD), U401.34 (VDD), U401.45 (VDD)
USBUP_VDD33: C407.1, C408.1, C409.1, C410.1, C411.1, C412.1, C413.1, C414.1, C415.1, C416.1, FB401.2, R406.2, R408.2, R410.2, R412.2, R414.2, R415.2, R416.2, R418.2, R420.2, R422.2, R424.2, U401.7 (VDD33), U401.13 (VDD33), U401.23 (VDD33), U401.25 (VDD33), U401.33 (VDD33), U401.37 (VDD33), U401.40 (VDD33), U401.48 (VDD33), U402.8 (VCC)

Notes on the sheet:
Resitors share share pad
Please close to the VCC pin
Place capacitors close to the VDD pins
Place capacitors close to the VDD33 pins
Place capacitors close to connector
